mjseabright/lampshades/photos/penta_spiral_fuzz-esun_blue-studio-front-light-on.jpg

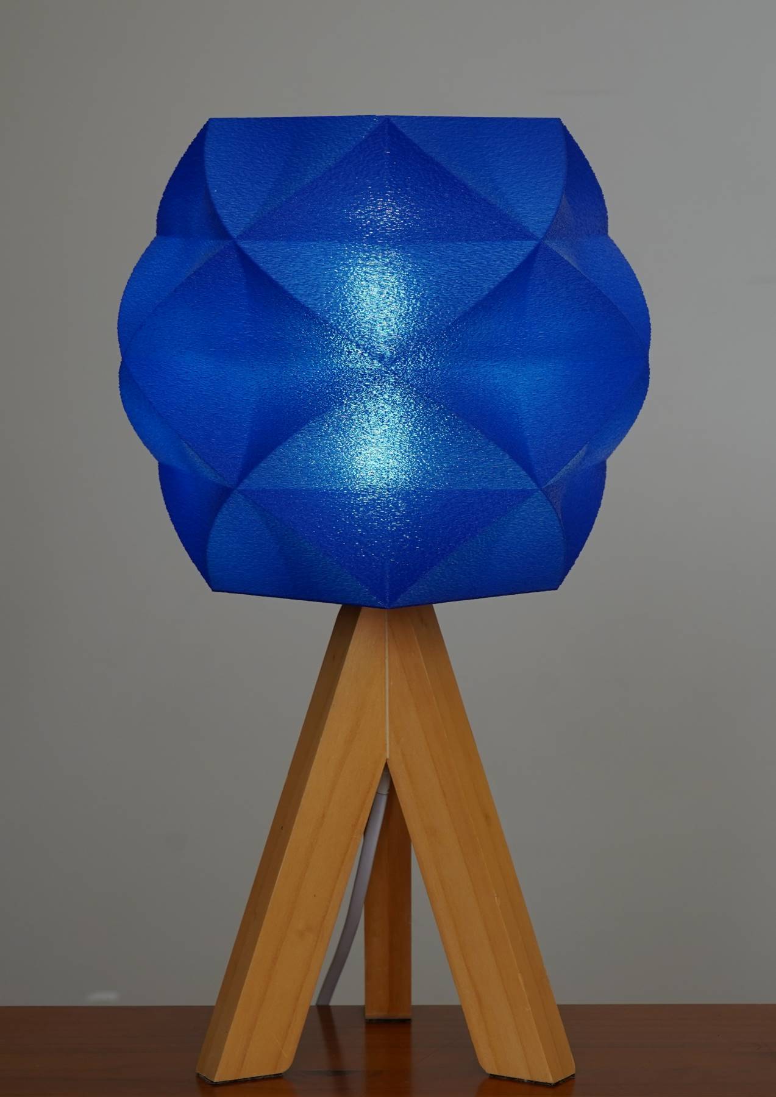
photos/penta_spiral_fuzz-esun_blue-studio-front-light-on.jpg
