mjseabright/lampshades/adaptor/adaptor.scad

rotate_extrude($fn=180) polygon([[18.5,0],
[27,0],
[27.5,0.5],
[27.5,1.5],
[27,2],
[20,2],
[20,30],
[18,32],
[14.5,32],
[14,31.5],
[14,30.5],
[14.5,30],
[16.5,30],
[16.5,2]]);
