mjseabright/lampshades/double_rotated_octagon/rotated_octogon_small.scad

use <rotated_octogon.scad>;
use <../mounting_functions.scad>;

height = 180;
layer_height = 0.2;
main_radius = 70;
center_hole_diameter = 40;

difference() {
    rotated_octogon(height = height, layer_height = layer_height, main_radius = main_radius);
    center_hole(height = height, diameter = center_hole_diameter);
}
