mjseabright/lampshades/noise/noisey.scad

CylinderPoints = [[65.0, 0.0, 0.0], [56.2917, 32.5, 0.0], [32.5, 56.2917, 0.0], [0.0, 65.0, 0.0], [-32.5, 56.2917, 0.0], [-56.2917, 32.5, 0.0], [-65.0, 0.0, 0.0], [-56.2917, -32.5, 0.0], [-32.5, -56.2917, 0.0], [-0.0, -65.0, 0.0], [32.5, -56.2917, 0.0], [56.2917, -32.5, 0.0], [83.2756, 22.3136, 45.0], [60.9619, 60.9619, 45.0], [22.3136, 83.2756, 45.0], [-22.3136, 83.2756, 45.0], [-60.9619, 60.9619, 45.0], [-83.2756, 22.3136, 45.0], [-83.2756, -22.3136, 45.0], [-60.9619, -60.9619, 45.0], [-22.3136, -83.2756, 45.0], [22.3136, -83.2756, 45.0], [60.9619, -60.9619, 45.0], [83.2756, -22.3136, 45.0], [95.0, 0.0, 90.0], [82.2724, 47.5, 90.0], [47.5, 82.2724, 90.0], [0.0, 95.0, 90.0], [-47.5, 82.2724, 90.0], [-82.2724, 47.5, 90.0], [-95.0, 0.0, 90.0], [-82.2724, -47.5, 90.0], [-47.5, -82.2724, 90.0], [-0.0, -95.0, 90.0], [47.5, -82.2724, 90.0], [82.2724, -47.5, 90.0], [83.2756, 22.3136, 135.0], [60.9619, 60.9619, 135.0], [22.3136, 83.2756, 135.0], [-22.3136, 83.2756, 135.0], [-60.9619, 60.9619, 135.0], [-83.2756, 22.3136, 135.0], [-83.2756, -22.3136, 135.0], [-60.9619, -60.9619, 135.0], [-22.3136, -83.2756, 135.0], [22.3136, -83.2756, 135.0], [60.9619, -60.9619, 135.0], [83.2756, -22.3136, 135.0], [65.0, 0.0, 180.0], [56.2917, 32.5, 180.0], [32.5, 56.2917, 180.0], [0.0, 65.0, 180.0], [-32.5, 56.2917, 180.0], [-56.2917, 32.5, 180.0], [-65.0, 0.0, 180.0], [-56.2917, -32.5, 180.0], [-32.5, -56.2917, 180.0], [-0.0, -65.0, 180.0], [32.5, -56.2917, 180.0], [56.2917, -32.5, 180.0], [0, 0, 0], [0, 0, 180]] ;
CylinderFaces = [[0, 12, 1], [1, 12, 13], [1, 13, 2], [2, 13, 14], [2, 14, 3], [3, 14, 15], [3, 15, 4], [4, 15, 16], [4, 16, 5], [5, 16, 17], [5, 17, 6], [6, 17, 18], [6, 18, 7], [7, 18, 19], [7, 19, 8], [8, 19, 20], [8, 20, 9], [9, 20, 21], [9, 21, 10], [10, 21, 22], [10, 22, 11], [11, 22, 23], [11, 23, 0], [12, 0, 23], [23, 24, 12], [12, 24, 25], [12, 25, 13], [13, 25, 26], [13, 26, 14], [14, 26, 27], [14, 27, 15], [15, 27, 28], [15, 28, 16], [16, 28, 29], [16, 29, 17], [17, 29, 30], [17, 30, 18], [18, 30, 31], [18, 31, 19], [19, 31, 32], [19, 32, 20], [20, 32, 33], [20, 33, 21], [21, 33, 34], [21, 34, 22], [22, 34, 35], [22, 35, 23], [23, 35, 24], [24, 36, 25], [25, 36, 37], [25, 37, 26], [26, 37, 38], [26, 38, 27], [27, 38, 39], [27, 39, 28], [28, 39, 40], [28, 40, 29], [29, 40, 41], [29, 41, 30], [30, 41, 42], [30, 42, 31], [31, 42, 43], [31, 43, 32], [32, 43, 44], [32, 44, 33], [33, 44, 45], [33, 45, 34], [34, 45, 46], [34, 46, 35], [35, 46, 47], [35, 47, 24], [36, 24, 47], [47, 48, 36], [36, 48, 49], [36, 49, 37], [37, 49, 50], [37, 50, 38], [38, 50, 51], [38, 51, 39], [39, 51, 52], [39, 52, 40], [40, 52, 53], [40, 53, 41], [41, 53, 54], [41, 54, 42], [42, 54, 55], [42, 55, 43], [43, 55, 56], [43, 56, 44], [44, 56, 57], [44, 57, 45], [45, 57, 58], [45, 58, 46], [46, 58, 59], [46, 59, 47], [47, 59, 48], [0, 1, 60], [49.0, 48.0, 61], [1, 2, 60], [50.0, 49.0, 61], [2, 3, 60], [51.0, 50.0, 61], [3, 4, 60], [52.0, 51.0, 61], [4, 5, 60], [53.0, 52.0, 61], [5, 6, 60], [54.0, 53.0, 61], [6, 7, 60], [55.0, 54.0, 61], [7, 8, 60], [56.0, 55.0, 61], [8, 9, 60], [57.0, 56.0, 61], [9, 10, 60], [58.0, 57.0, 61], [10, 11, 60], [59.0, 58.0, 61], [11, 0, 60], [48.0, 59.0, 61]] ;
difference() {
    polyhedron( CylinderPoints, CylinderFaces, convexity = 10);
    translate([0,0,-10]) linear_extrude(200) circle(d=40, $fa=1);
}
