mjseabright/lampshades/rope_swirl/rope_swirl_large_base.scad

use <../bases/low_pro_with_adaptor.scad>;

// Copied from rope_swirl_large.scad -- keep these in sync with that file so
// the base's spokes/foot holes/mount bore line up with the shade.
num_feet = 3;             // number of spokes/feet; must match num_feet in rope_swirl_large.scad
foot_hole_diameter = 4.5; // must match foot_hole_diameter in rope_swirl_large.scad (mm)
foot_hole_radius = 85;    // must match foot_hole_radius in rope_swirl_large.scad (mm)
mount_od = 40;            // outer diameter of the central adaptor-mount boss; must match center_hole_diameter in rope_swirl_large.scad (mm)

spoke_width = 10;          // width of each spoke at its tip, i.e. at the foot-mounting hole (mm)
spoke_width_center = 15;  // width of each spoke at the center mount, tapering down to spoke_width at the tip (mm)
spoke_height = 2;         // height of each spoke (mm)
mount_id = 33;            // inner diameter of the central adaptor-mount boss, i.e. the bore the adaptor sits in (mm)
mount_height = 65;         // height of the central adaptor-mount boss (mm)
mount_hole_diameter = 28; // diameter of the fixing hole(s) through the mount boss (mm)

low_pro_with_adaptor(
    num_spokes = num_feet,
    foot_hole_diameter = foot_hole_diameter,
    foot_hole_radius = foot_hole_radius,
    spoke_width = spoke_width,
    spoke_width_center = spoke_width_center,
    spoke_height = spoke_height,
    mount_od = mount_od,
    mount_id = mount_id,
    mount_height = mount_height,
    mount_hole_diameter = mount_hole_diameter
);
